openretroMGB/OpenRetroMGB/assets/ardunio_cart_bottom.png

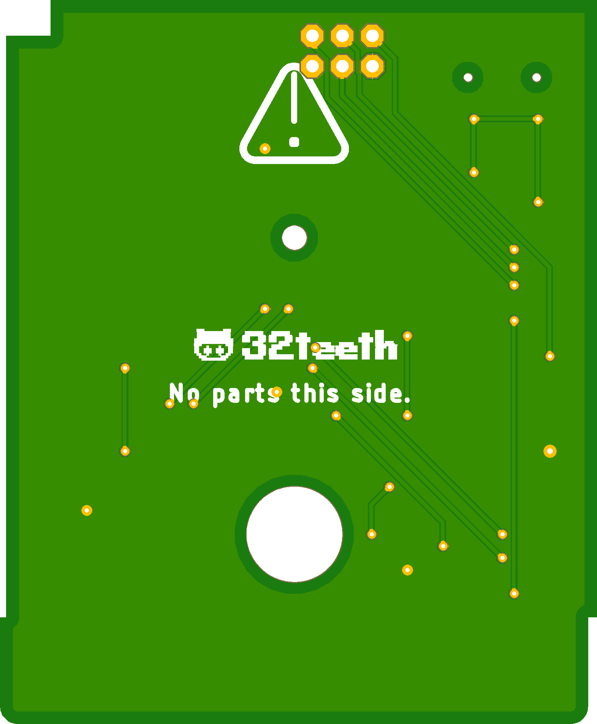
assets/ardunio_cart_bottom.png
