openretroMGB/OpenRetroMGB/assets/ardunio_cart_top.png

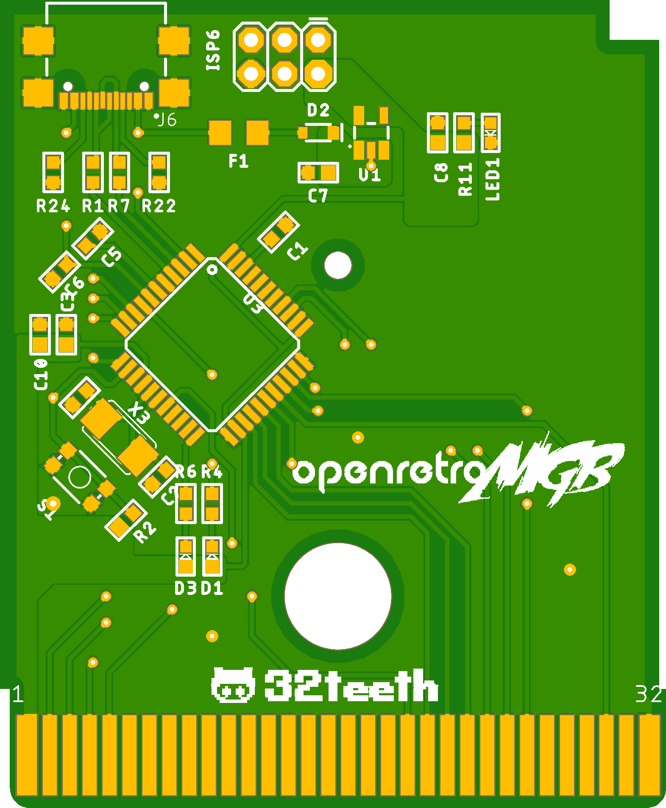
assets/ardunio_cart_top.png
