openretroMGB/OpenRetroMGB/assets/fit+finish.png

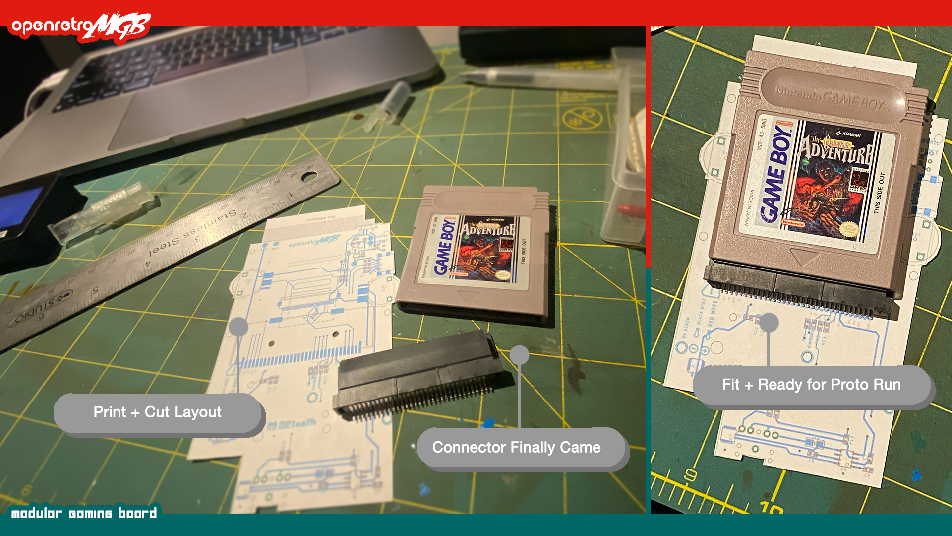
assets/fit+finish.png
