openretroMGB/OpenRetroMGB/assets/lcd.png

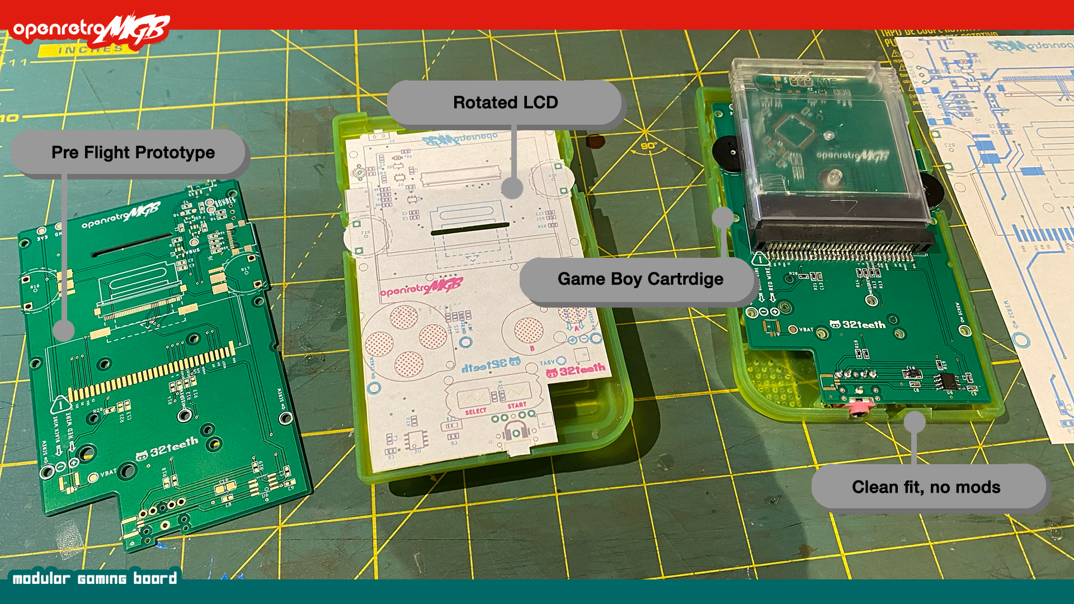
assets/lcd.png
