openretroMGB/OpenRetroMGB/assets/mainboard_bottom.png

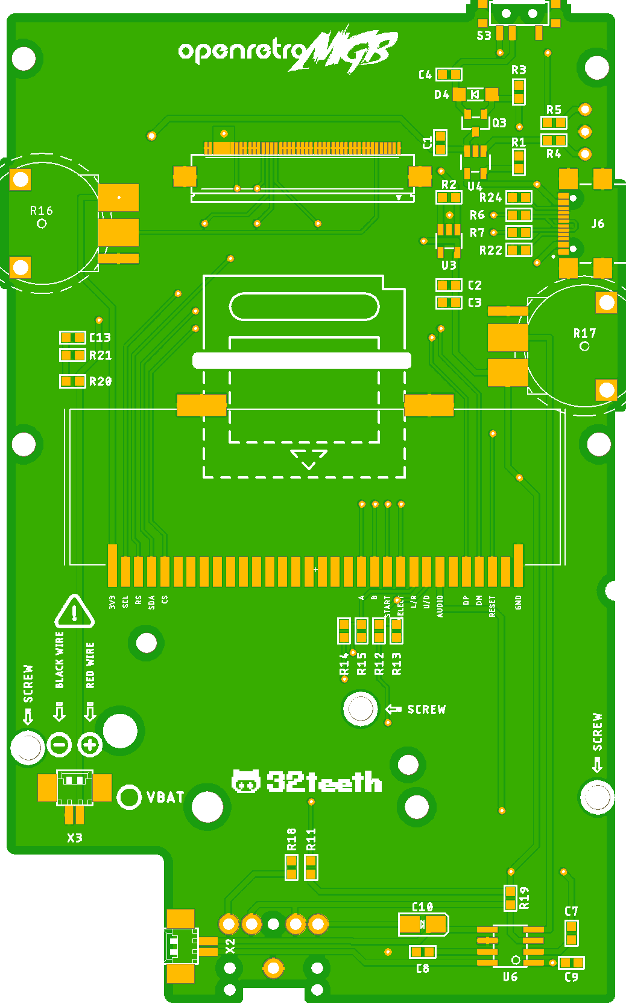
assets/mainboard_bottom.png
