openretroMGB/OpenRetroMGB/assets/mainboard_option.png

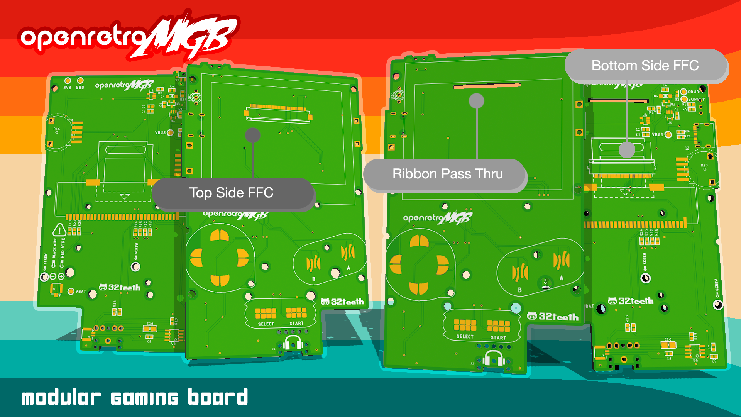
assets/mainboard_option.png
