openretroMGB/OpenRetroMGB/assets/mainboard_top.png

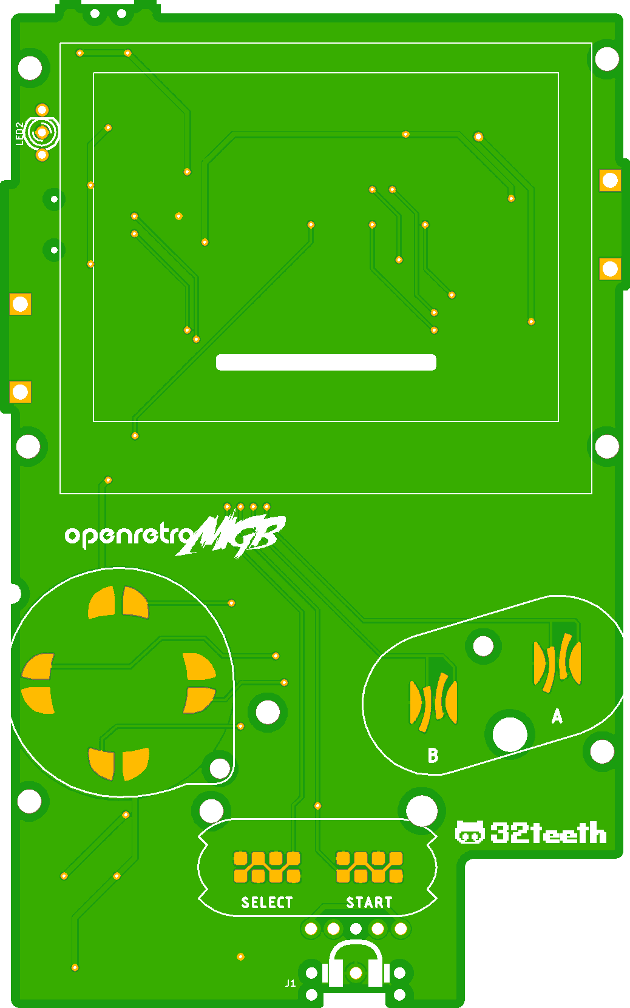
assets/mainboard_top.png
