openretroMGB/OpenRetroMGB/assets/retro_cart_top.png

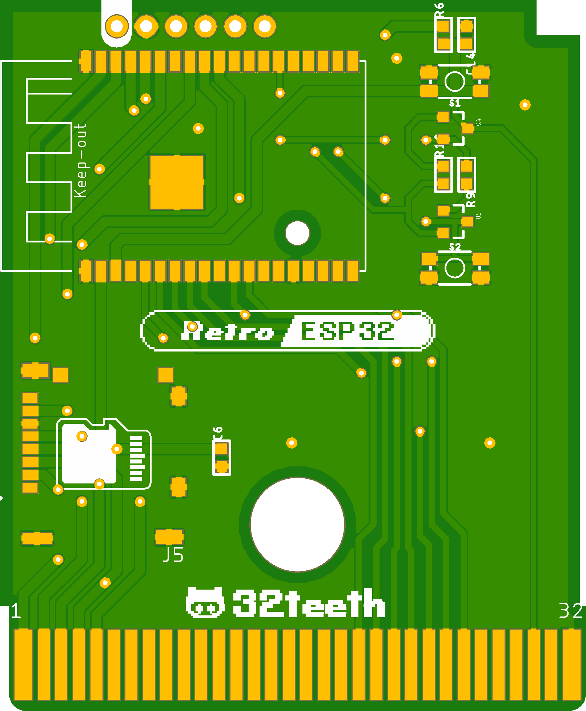
assets/retro_cart_top.png
