openretroMGB/OpenRetroMGB/assets/sponsor.png

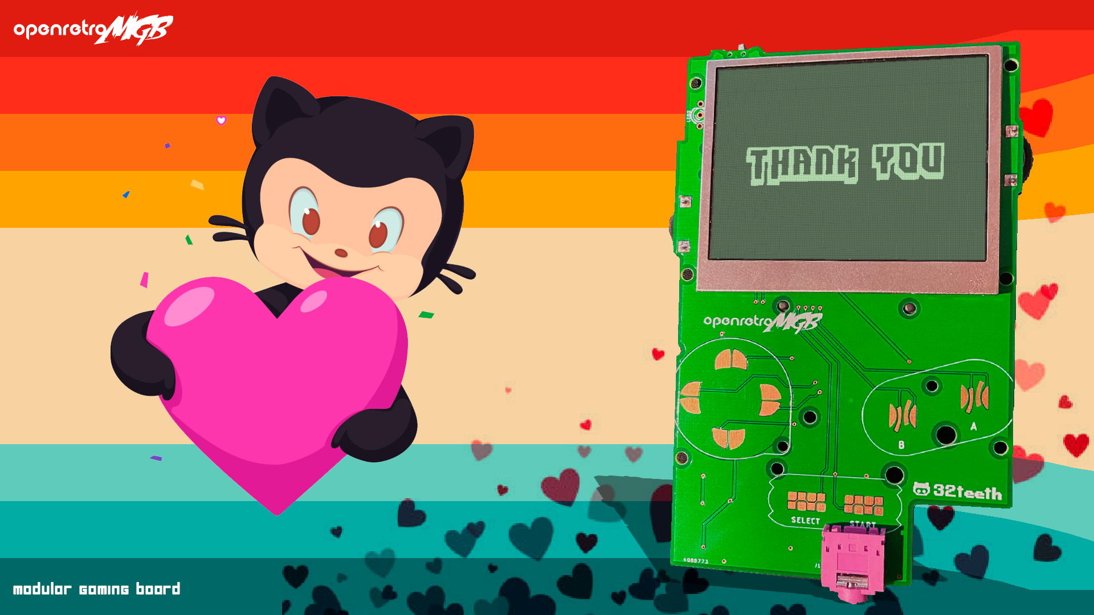
assets/sponsor.png
